jrengdahl/H503/Core/Src/serial.cpp

// gaskets which adapt the serial I/O system (i.e. USB VCP) to printf and getline

// Copyright (c) 2009, 2023 Jonathan Engdahl
// BSD license -- see the accompanying LICENSE file

 
#include <stdint.h>
#include "main.h"
#include "context.hpp"
#include "Fifo.hpp"
#include "ContextFIFO.hpp"
#include "Port.hpp"
#include "CriticalRegion.hpp"
#include "usbd_cdc_if.h"
#include "tim.h"

extern "C" const char *strnchr(const char *s, int n, int c);

Port txPort;
Port rxPort;

FIFO<char, 64> ConsoleFifo;

bool ControlC = false;
bool SerialRaw = false;

extern "C"
int __io_kbhit()                                // test for input
    {
    if(ConsoleFifo)
        {
        return 1;
        }
    else
        {
        return 0;
        }
    }


extern "C"
int __io_getchar()                              // link the CMSIS syslib to the HAL's UART input
    {
    char ch;

    do
        {
        CRITICAL_REGION(InterruptLock)          // close the window between test and wait, where a callback might occur
            {
            if(!ConsoleFifo)
                {
                rxPort.suspend();
                yield();
                }
            }
        }
    while(!ConsoleFifo.take(ch));

    return ch;
    }


extern "C"
int __io_getchart(unsigned timeout)                      // getch with timeout
    {
    char ch;
    uint32_t start = __HAL_TIM_GET_COUNTER(&htim2);

    do
        {
        if(ConsoleFifo)
            {
            ConsoleFifo.take(ch);

            return ch;
            }
        yield();
        }
    while(__HAL_TIM_GET_COUNTER(&htim2) - start < timeout);
    return -1;
    }


// refactored code: atomically wrap the test and wait for txready, then output the buffer
static void vcp_writeblock(uint8_t* Buf1, uint16_t Len1, uint8_t* Buf2 = 0, uint16_t Len2 = 0)
    {
    do
        {
        CRITICAL_REGION(InterruptLock)                          // test for busy and wait atomically
            {
            if(!vcp_txready())
                {
                txPort.suspend();                                  // so the callback cannot occur in the window between the test and wait
                yield();
                }
            }
        }
    while(CDC_Transmit_FS(Buf1, Len1, Buf2, Len2) == USBD_BUSY);
    }

extern "C"
int _write(int file, const char *ptr, int len)
    {
    int retlen = len;                                           // success return = buffer len

    while(len)                                                  // while there is some of the buffer left
        {
        const char *pnl;                                        // pointer to newline

        pnl = strnchr(ptr, len, '\n');                          // see if there is a newline in the buffer
        if(pnl )
            {
            vcp_writeblock((uint8_t *)ptr, pnl-ptr, (uint8_t *)"\r\n", 2); // if so, output the buffer up to before the newlin, followed by return and newline

            len -= pnl-ptr+1;                                   // skip over the newline in the buffer
            ptr = pnl+1;
            }                                                   // we will repeat until the buffer is empty
        else                                                    // if there is no newline
            {
            vcp_writeblock((uint8_t *)ptr, len);                // just output the whole buffer

            len = 0;                                            // and set the len to zero so there is no repeat
            }
        }

    return retlen;
    }


extern "C"
int _writenl(int file, const char *ptr, int len)
    {
    vcp_writeblock((uint8_t *)ptr, len, (uint8_t *)"\r\n", 2);
    return len;
    }


extern "C"
void vcp_tx_callback()
    {
    txPort.resume();
    }

extern "C"
void vcp_rx_callback(uint8_t *Buf, uint32_t Len)
    {
    for(unsigned i=0; i<Len; i++)
        {
        char ch = Buf[i];

        if(ch == 'C'-'@' && !SerialRaw)
            {
            ControlC = true;
            }
        else
            {
            ConsoleFifo.add(ch);
            rxPort.resume();
            }
        }

    }
