jrengdahl/H503/Core/Src/StrCommand.cpp

#include <stdio.h>
#include <string.h>
#include <ctype.h>
#include <math.h>
#include "local.h"
#include "main.h"
#include "cmsis.h"


void StrCommand(char *p)
    {
    uint32_t value = gethex(&p);
    skip(&p);
    uintptr_t addr = gethex(&p);            // get the address

    __asm__ __volatile__(
            "str %0, [%1]       \n\t"
            "dsb SY"
    :
    : "r"(value), "r"(addr)
    : );
    }
