jrengdahl/H503/Core/Inc/ThreadFIFO.hpp

// threadFIFO
//
// A threadFIFO is a subclass of FIFO. The data type stored in the FIFO are Threads.
// The inherited member functions add and take are not much use.
// The subclass member functions, suspend and resume, enable multiple threads to suspend at
// a threadFIFO. When a threadFIFO is resumed the oldest suspended thread is resumed.
// One notable use of a threadFIFO is the DeferFIFO, which is used to support yield and
// timesharing among multiple threads.

// Copyright (c) 2023 Jonathan Engdahl
// BSD license -- see the accompanying LICENSE file




#ifndef THREADFIFO_HPP
#define THREADFIFO_HPP

#include "cmsis.h"
#include "thread.hpp"
#include "FIFO.hpp"

static const unsigned THREAD_FIFO_DEPTH = 15;    // must be a power of 2, minus 1, if this is changed, the inline ASM must be updated

class ThreadFIFO : public FIFO<Thread, THREAD_FIFO_DEPTH>
    {
    public:

    bool suspend();
    void suspend_switch();
    bool resume();
    void resume_switch();
    };


extern ThreadFIFO DeferFIFO;


// suspend the current thread at the DeferFIFO.
// It will be resumed later by the background thread.
// If the DeferFIFO is full yield will simply return immediately without yielding.

static inline void yield()
    {
    DeferFIFO.suspend();
    }


// Called by the backgroud thread to resume any supended threads in the DeferFIFO.
// If the DeferFIFO is empty this routine does nothing.

static inline void undefer()
    {
    DeferFIFO.resume();
    }


#endif // THREADFIFO_HPP
